insolace/Playback-Wing/IMG/bot-lcd2.png

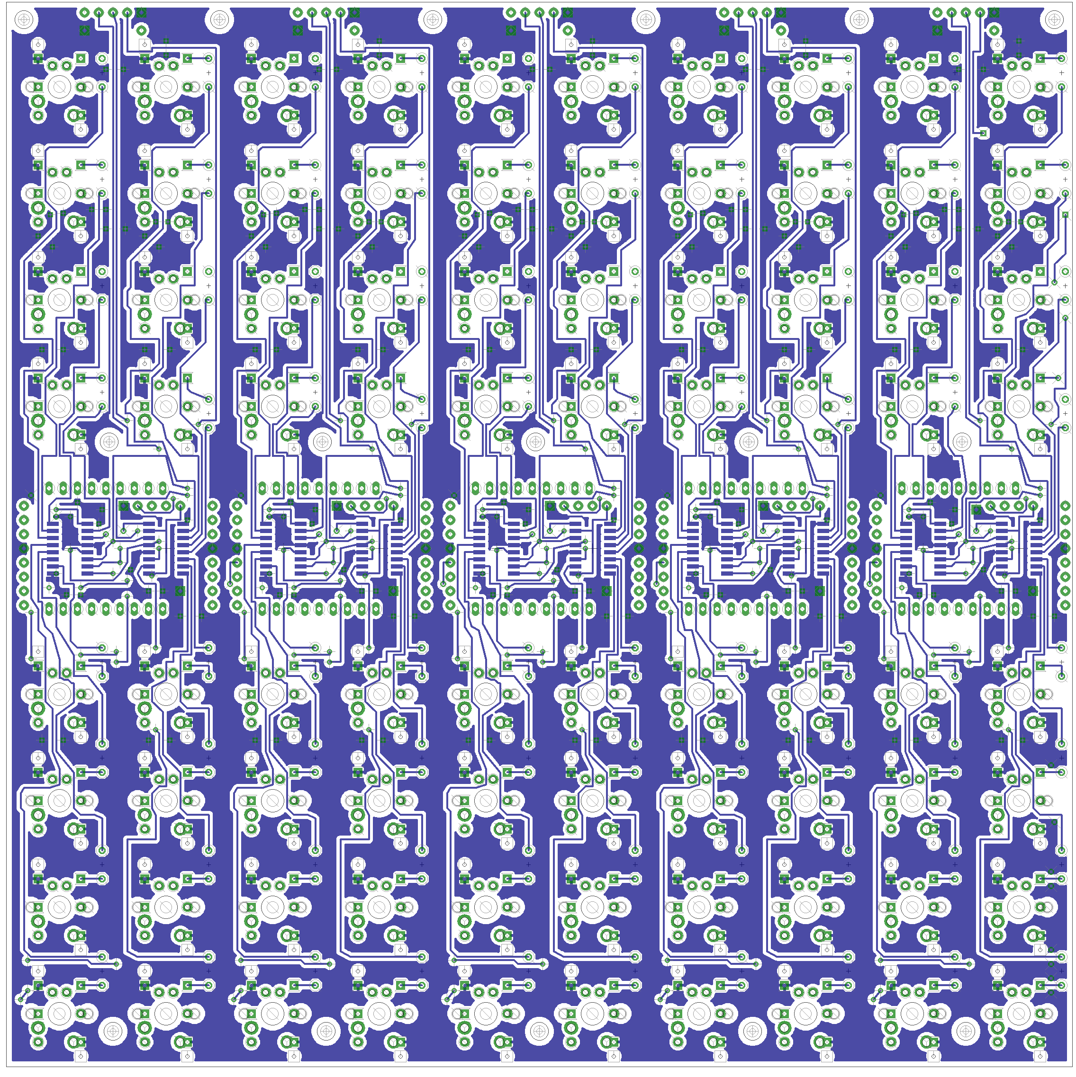
IMG/bot-lcd2.png
