insolace/Playback-Wing/IMG/schem.png

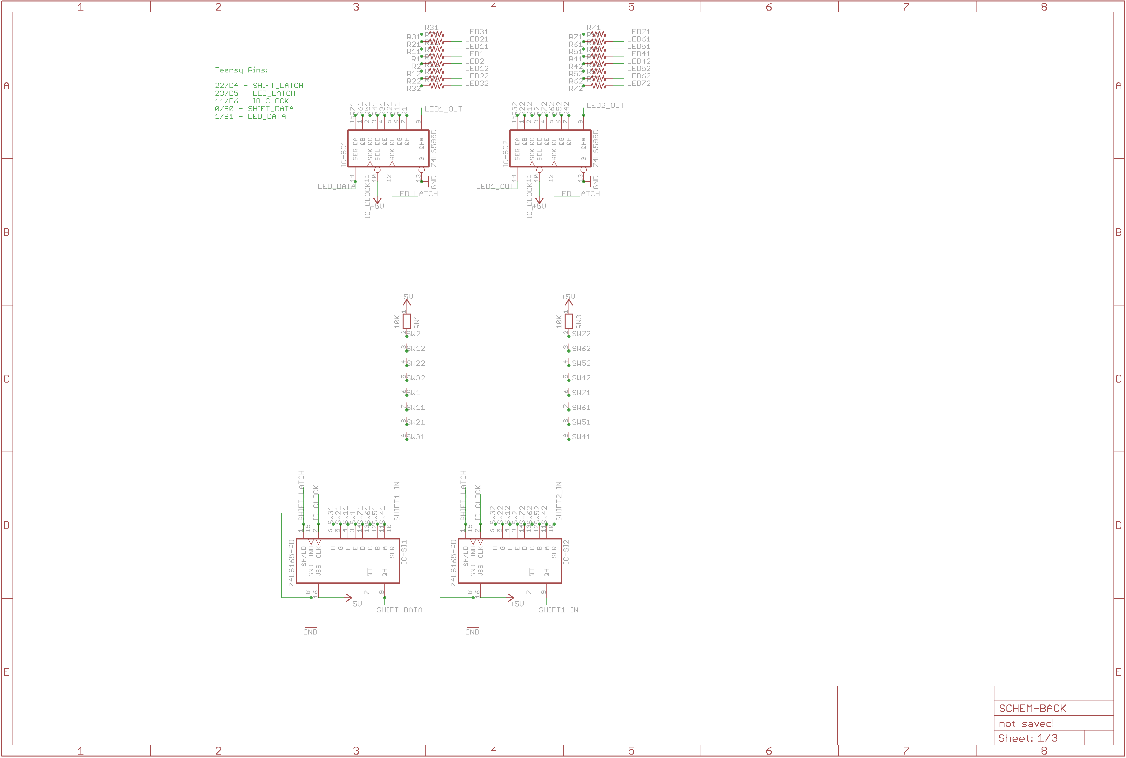
IMG/schem.png
