insolace/Playback-Wing/IMG/top.png

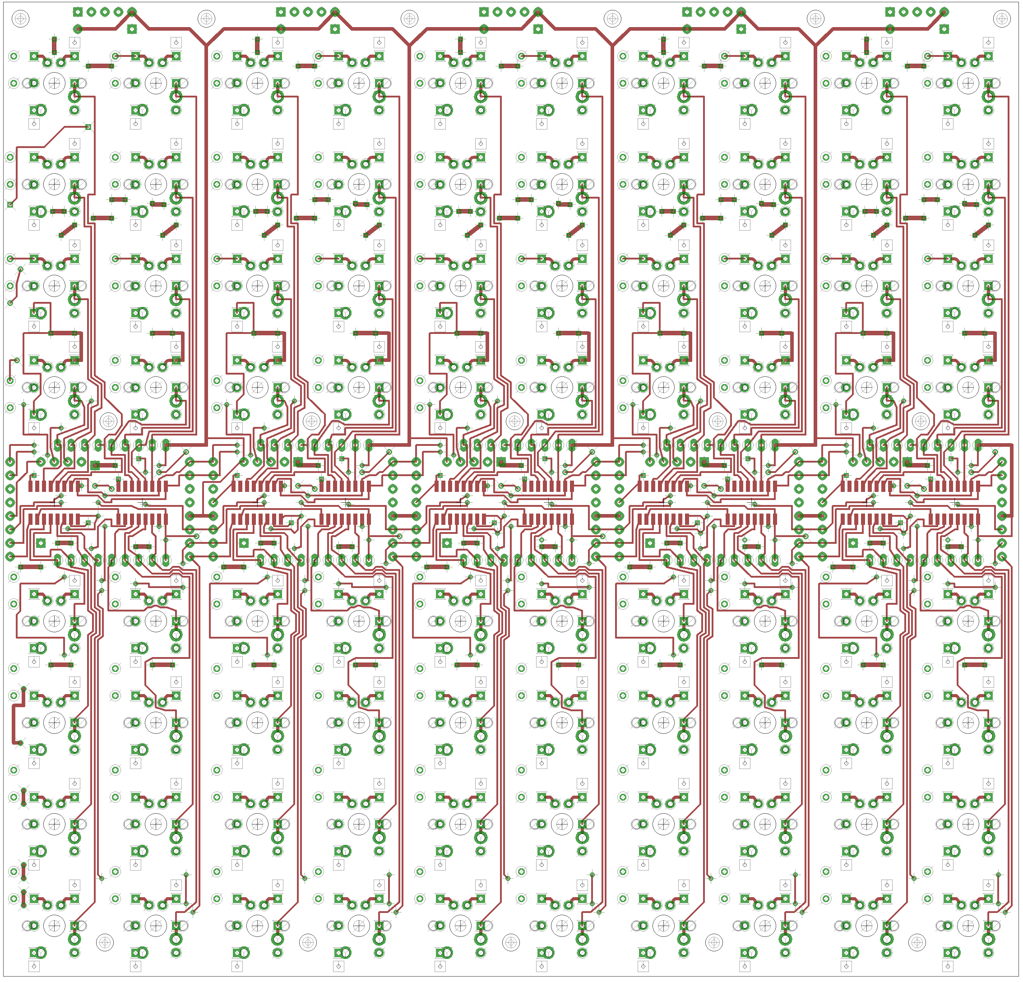
IMG/top.png
